arithmaldor/SCART-Splitter/Renders/Bottom.png

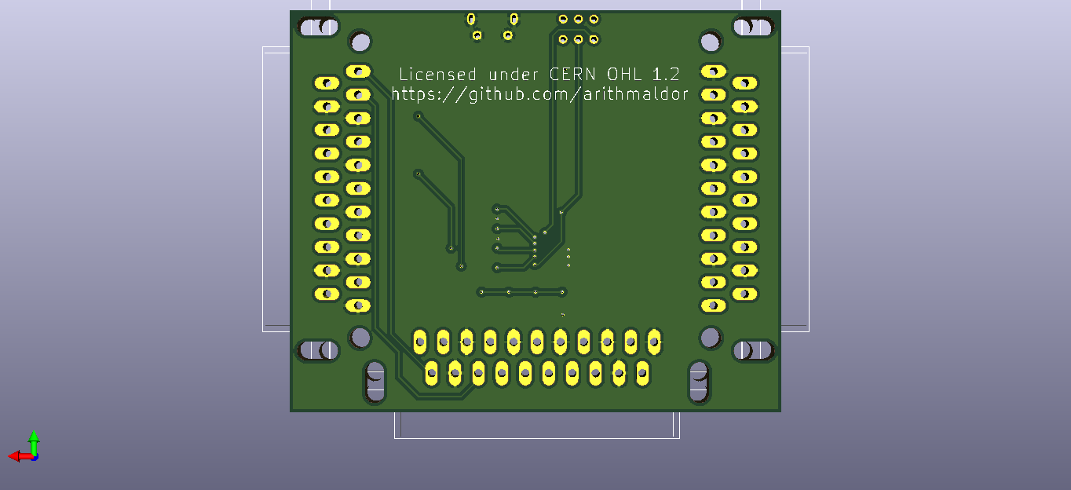
Renders/Bottom.png
