arithmaldor/SCART-Splitter/Case/Scart Splitter Case Measurements.png

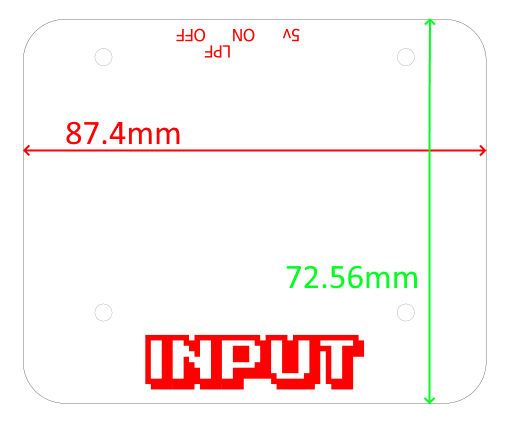
Case/Scart Splitter Case Measurements.png
